KM101304/Cyberdeck-ferris-/docs/assets/previews/fielddeck_closed_iso.png

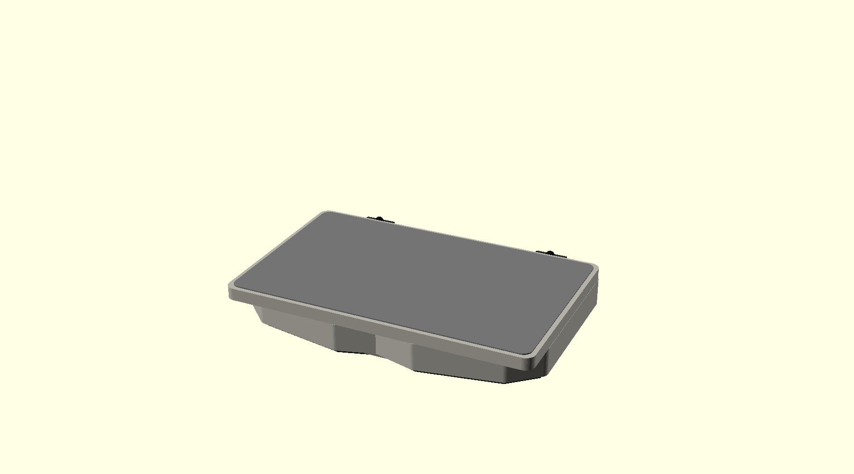
docs/assets/previews/fielddeck_closed_iso.png
