KM101304/Cyberdeck-ferris-/docs/assets/previews/fielddeck_keyboard_iso.png

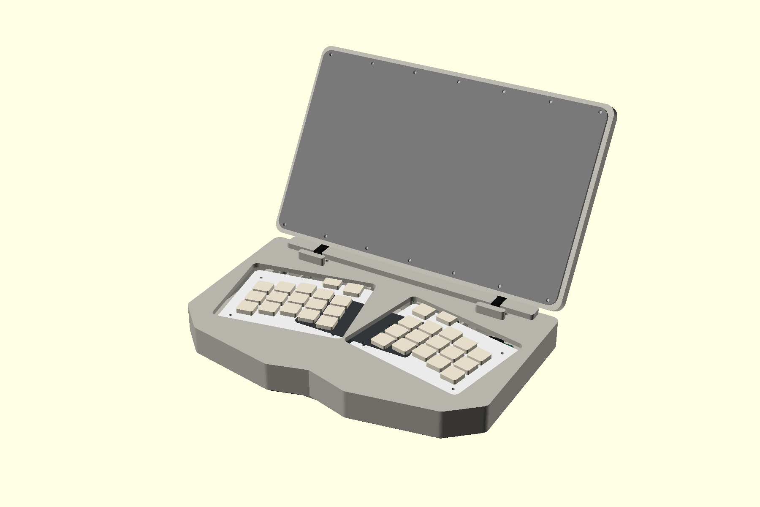
docs/assets/previews/fielddeck_keyboard_iso.png
