KM101304/Cyberdeck-ferris-/docs/assets/previews/fielddeck_keyboard_top.png

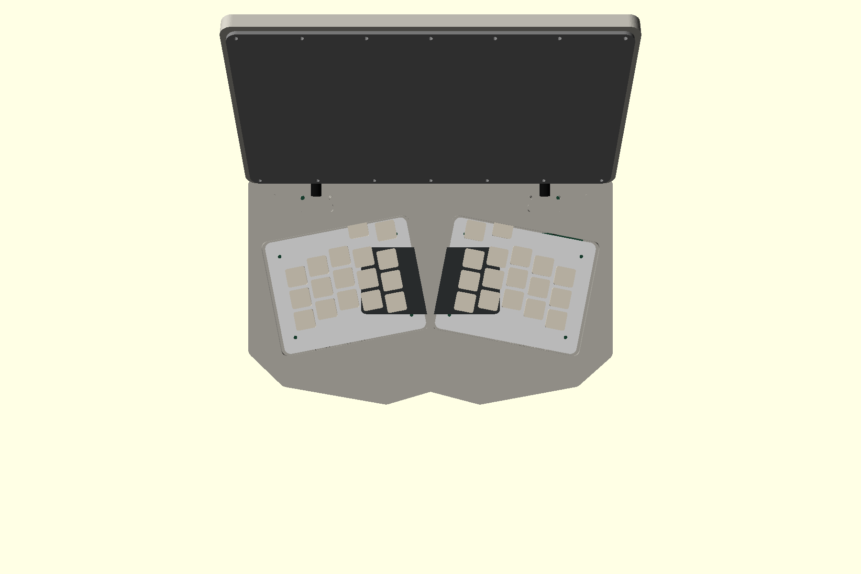
docs/assets/previews/fielddeck_keyboard_top.png
