KM101304/Cyberdeck-ferris-/docs/assets/previews/fielddeck_open_front.png

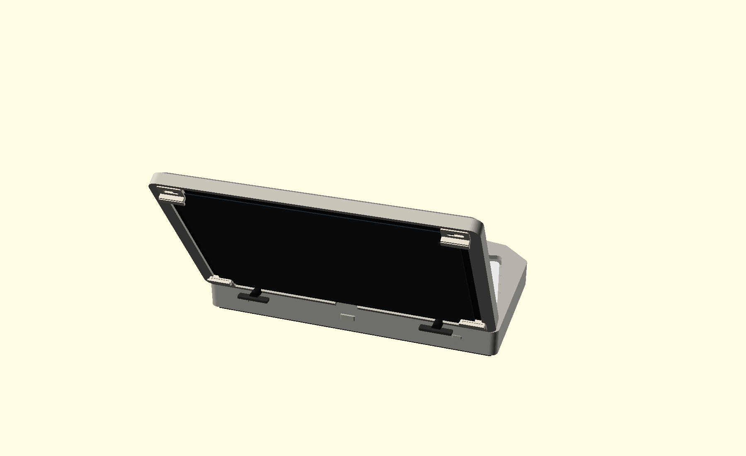
docs/assets/previews/fielddeck_open_front.png
