KM101304/Cyberdeck-ferris-/docs/assets/previews/fielddeck_open_side.png

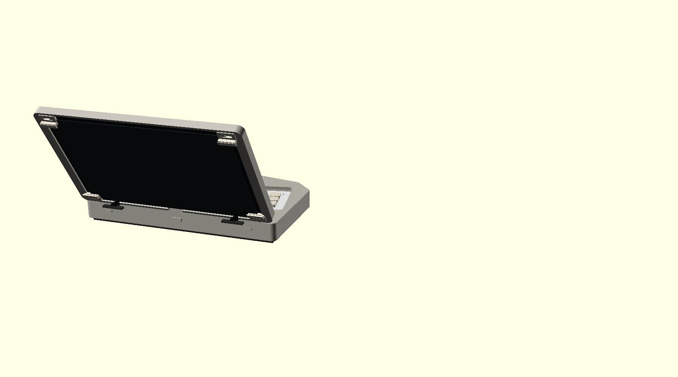
docs/assets/previews/fielddeck_open_side.png
