KM101304/Cyberdeck-ferris-/exports/stl/bottom_cover.stl

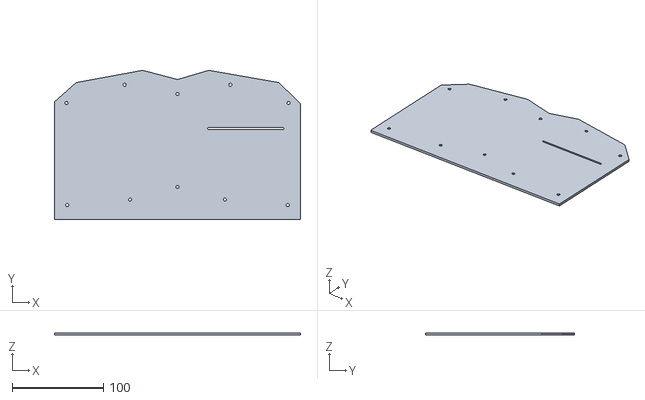
[picture p38: CAD file, 2026-05-10]
exports/stl/bottom_cover.stl
270.0 x 163.8 x 2.60
