KM101304/Cyberdeck-ferris-/exports/stl/cable_cover_long.stl

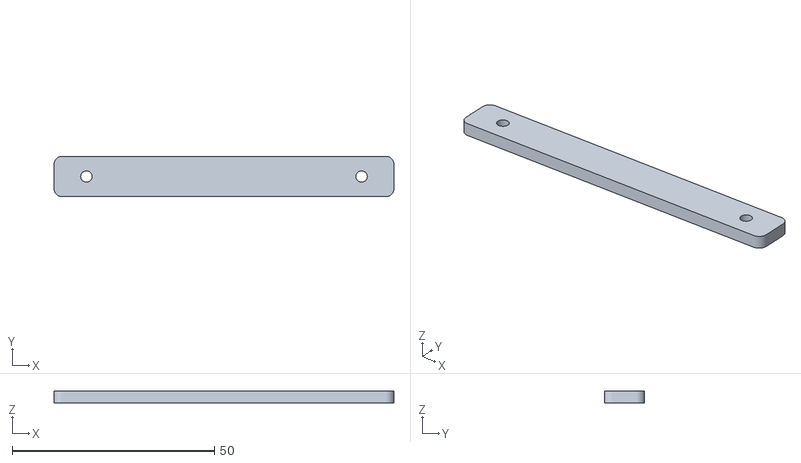
[picture p39: CAD file, 2026-05-10]
exports/stl/cable_cover_long.stl
84.0 x 10.0 x 3.00
