KM101304/Cyberdeck-ferris-/exports/stl/tablet_bracket.stl

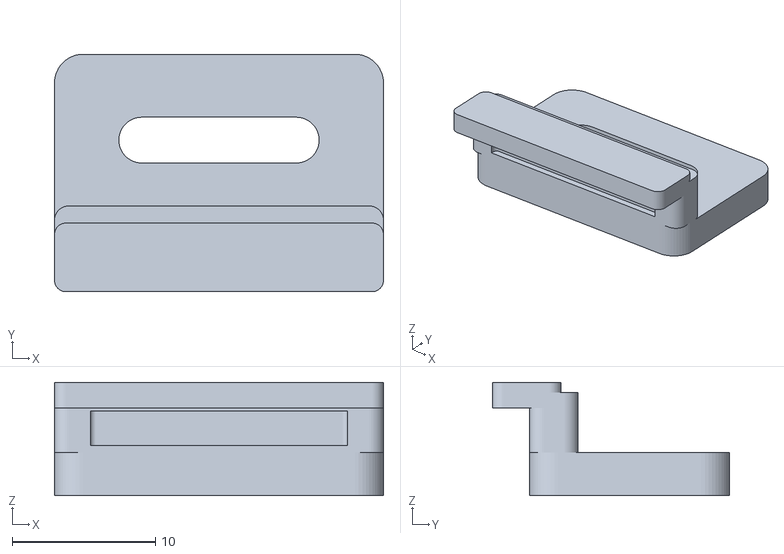
[picture p40: CAD file, 2026-05-10]
exports/stl/tablet_bracket.stl
23.0 x 16.6 x 7.90
