KM101304/Cyberdeck-ferris-/exports/stl/cable_cover_short.stl

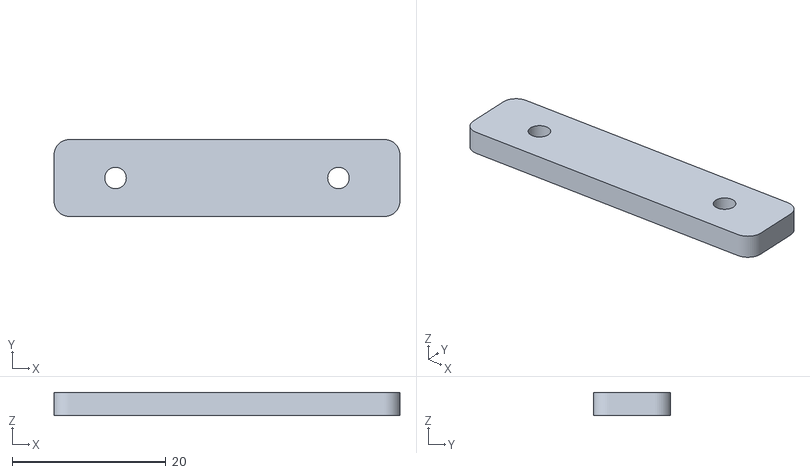
[picture p41: CAD file, 2026-05-09]
exports/stl/cable_cover_short.stl
45.0 x 10.0 x 3.00
