KM101304/Cyberdeck-ferris-/scad/parts/assembly_preview.scad

PART = "assembly_preview";
include <../fielddeck.scad>;
