KM101304/Cyberdeck-ferris-/scad/parts/battery_strap.scad

PART = "battery_strap";
include <../fielddeck.scad>;
