KM101304/Cyberdeck-ferris-/scad/parts/bottom_cover.scad

PART = "bottom_cover";
include <../fielddeck.scad>;
