KM101304/Cyberdeck-ferris-/scad/parts/cable_cover_long.scad

PART = "cable_cover_long";
include <../fielddeck.scad>;
