KM101304/Cyberdeck-ferris-/scad/parts/cable_cover_short.scad

PART = "cable_cover_short";
include <../fielddeck.scad>;
