KM101304/Cyberdeck-ferris-/scad/parts/closed_preview.scad

PART = "closed_preview";
include <../fielddeck.scad>
