KM101304/Cyberdeck-ferris-/scad/parts/fit_coupon.scad

PART = "fit_coupon";
include <../fielddeck.scad>;
