KM101304/Cyberdeck-ferris-/scad/parts/lower_hinge_block_left.scad

PART = "lower_hinge_block_left";
include <../fielddeck.scad>;
