KM101304/Cyberdeck-ferris-/scad/parts/lower_hinge_block_right.scad

PART = "lower_hinge_block_right";
include <../fielddeck.scad>;
