KM101304/Cyberdeck-ferris-/scad/parts/lower_left.scad

PART = "lower_left";
include <../fielddeck.scad>;
