KM101304/Cyberdeck-ferris-/scad/parts/lower_right.scad

PART = "lower_right";
include <../fielddeck.scad>;
