KM101304/Cyberdeck-ferris-/scad/parts/tablet_bracket.scad

PART = "tablet_bracket";
include <../fielddeck.scad>;
