KM101304/Cyberdeck-ferris-/scad/parts/upper_hinge_block_left.scad

PART = "upper_hinge_block_left";
include <../fielddeck.scad>;
