KM101304/Cyberdeck-ferris-/scad/parts/upper_hinge_block_right.scad

PART = "upper_hinge_block_right";
include <../fielddeck.scad>;
