KM101304/Cyberdeck-ferris-/scad/parts/upper_lid_back.scad

PART = "upper_lid_back";
include <../fielddeck.scad>;
