KM101304/Cyberdeck-ferris-/scad/parts/upper_lid_frame.scad

PART = "upper_lid_frame";
include <../fielddeck.scad>;
