KM101304/Cyberdeck-ferris-/scad/parts/web_components.scad

PART = "web_components";
include <../fielddeck.scad>;
