KM101304/Cyberdeck-ferris-/scad/parts/web_keycaps.scad

PART = "web_keycaps";
include <../fielddeck.scad>;
