KM101304/Cyberdeck-ferris-/scad/parts/web_shell.scad

PART = "web_shell";
include <../fielddeck.scad>;
