KM101304/Cyberdeck-ferris-/scad/parts/web_tablet.scad

PART = "web_tablet";
include <../fielddeck.scad>;
